l1tran/RMS/Images/Blynk 2.PNG

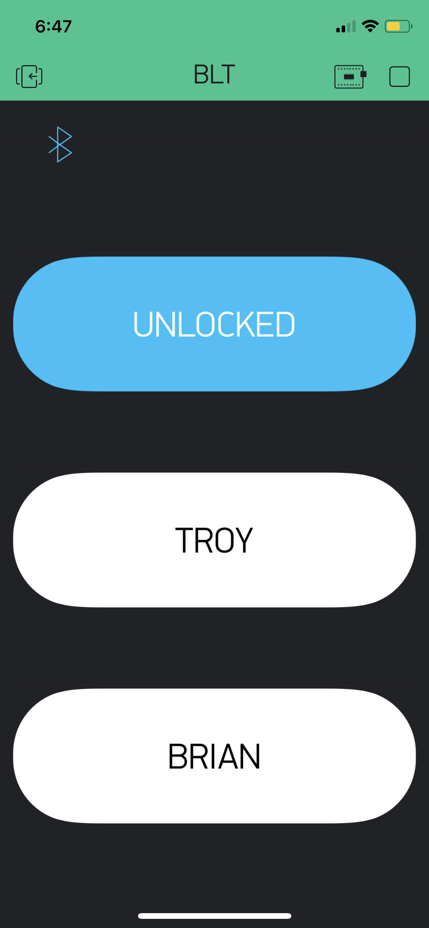
Images/Blynk 2.PNG
